benpeart/ada/images/_1a1928ad-4c3a-4578-ae90-0e928d0e105a.jpg

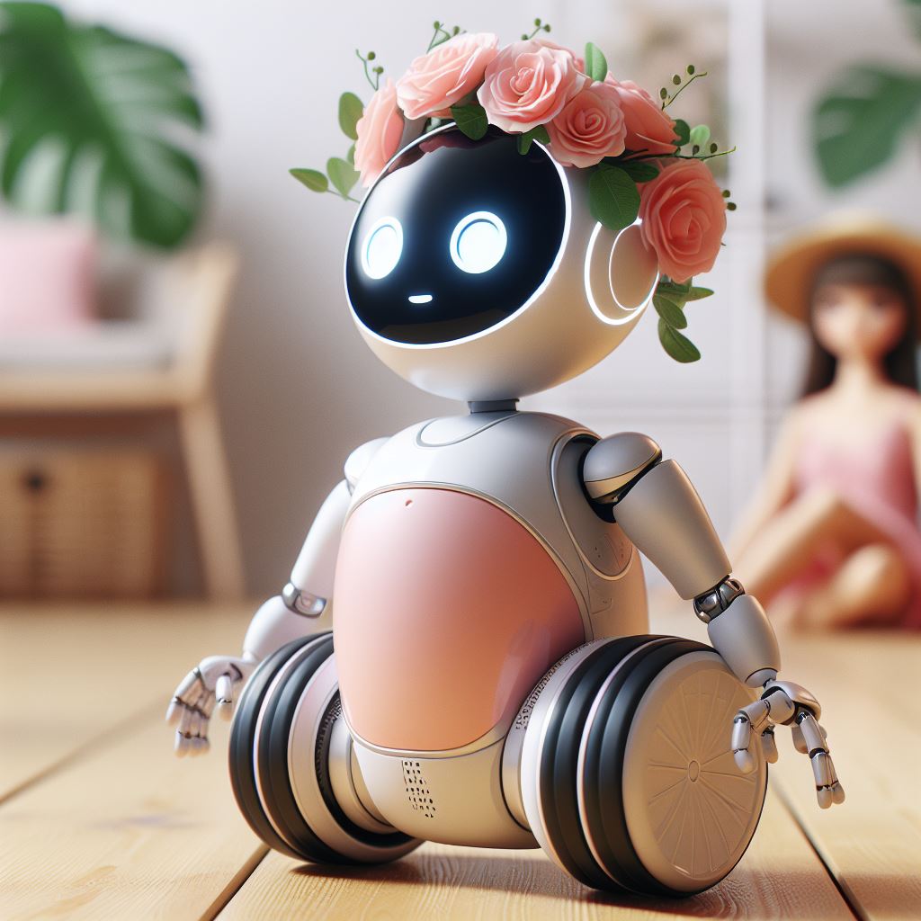
images/_1a1928ad-4c3a-4578-ae90-0e928d0e105a.jpg
