benpeart/ada/images/_2ccc8184-fcf1-47fc-b488-26bac7fec8c7.jpg

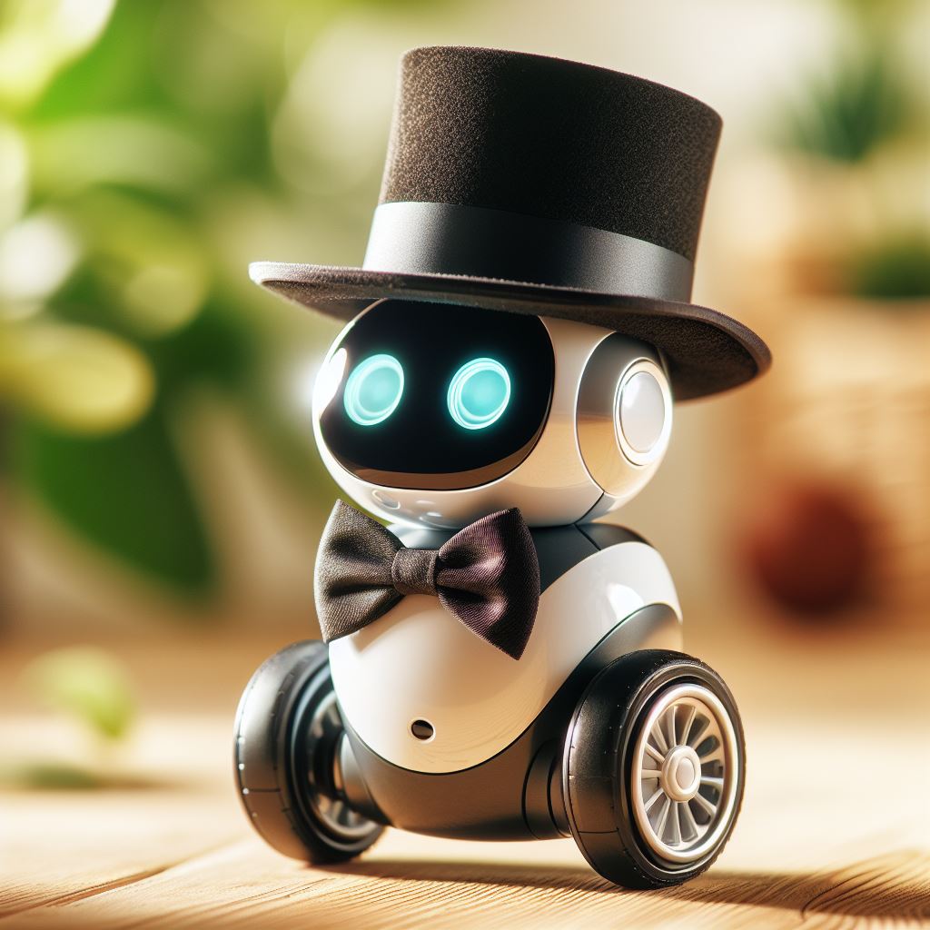
images/_2ccc8184-fcf1-47fc-b488-26bac7fec8c7.jpg
