benpeart/ada/images/_25c779a2-1914-4023-8b9f-634e2caacfa5.jpg

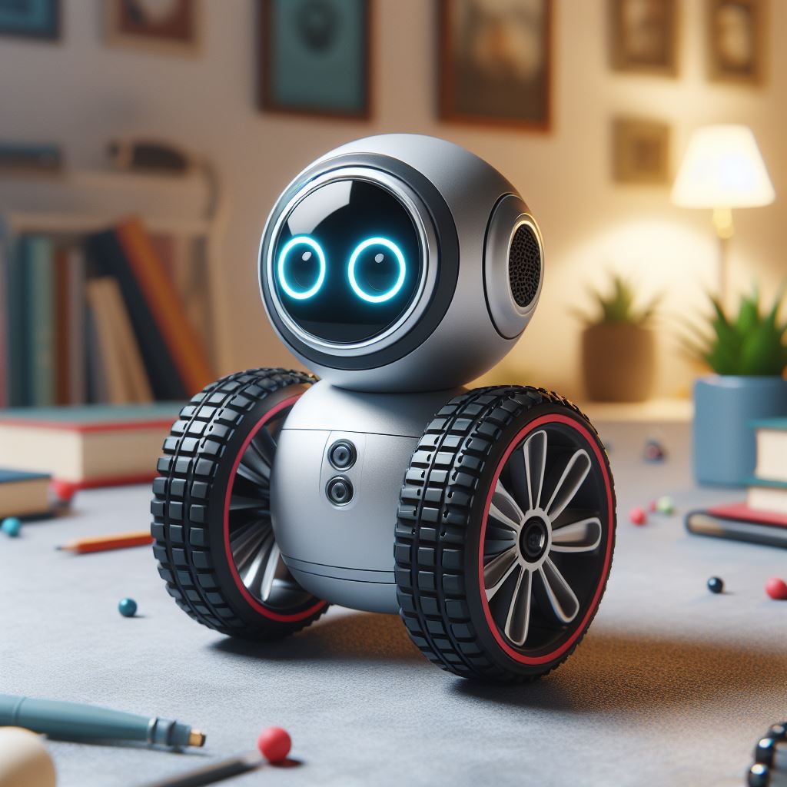
images/_25c779a2-1914-4023-8b9f-634e2caacfa5.jpg
