benpeart/ada/images/_547f5dd5-d0b9-4bb5-aa50-cecd44a33f60.jpg

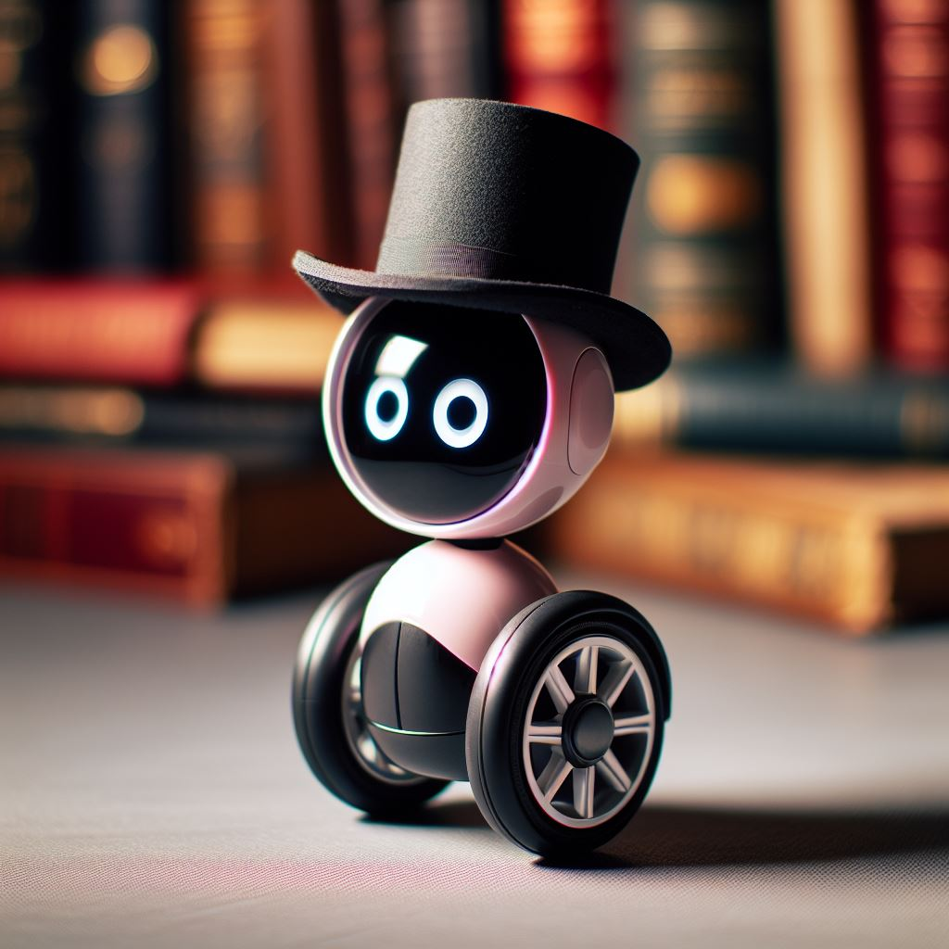
images/_547f5dd5-d0b9-4bb5-aa50-cecd44a33f60.jpg
