benpeart/ada/images/_3496c268-cb07-46fb-8d25-417b17f914ac.jpg

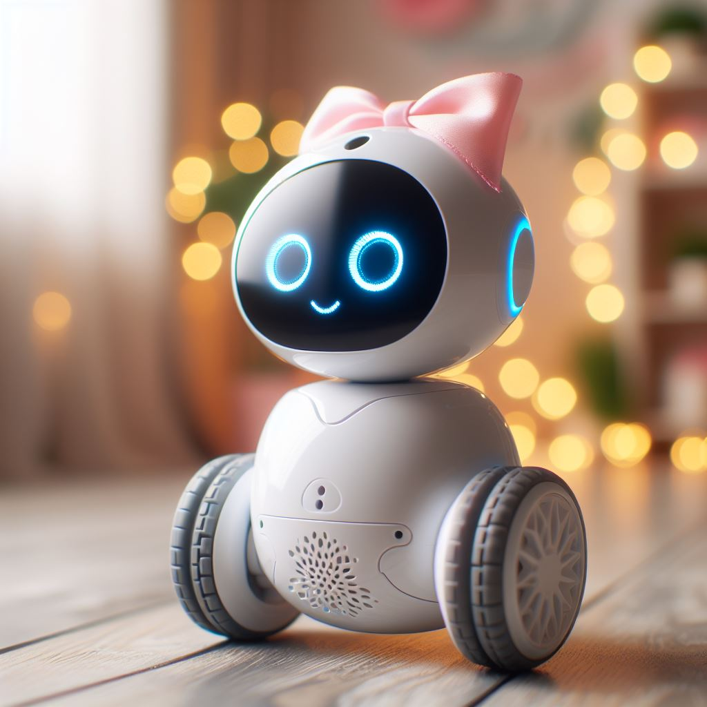
images/_3496c268-cb07-46fb-8d25-417b17f914ac.jpg
