benpeart/ada/images/_54363b42-9e46-489c-88c6-ef07b5f35076.jpg

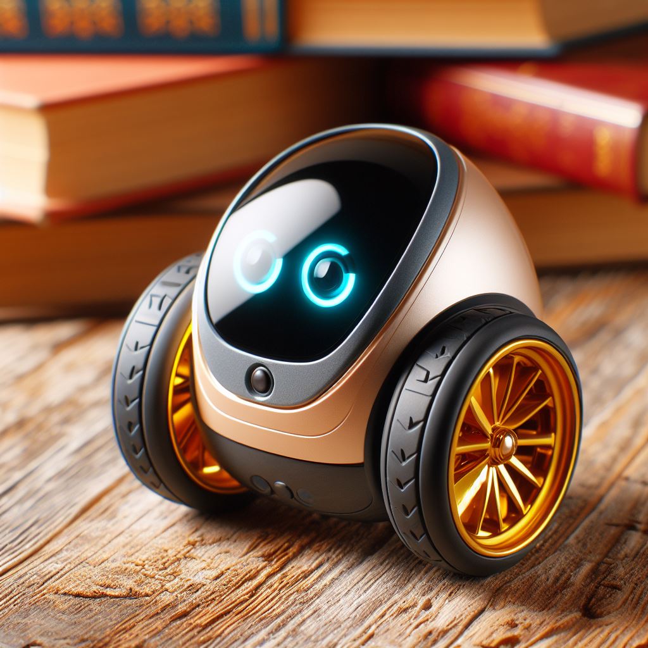
images/_54363b42-9e46-489c-88c6-ef07b5f35076.jpg
