benpeart/ada/images/_815840c3-b298-4146-8053-1009c332dad5.jpg

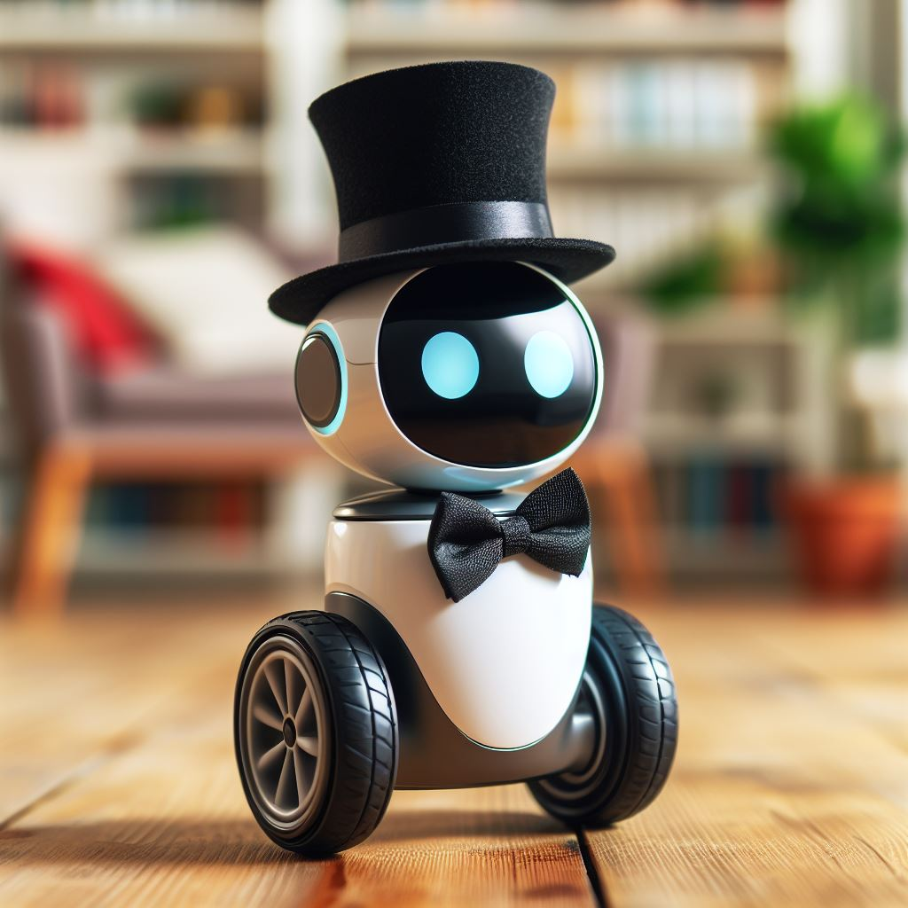
images/_815840c3-b298-4146-8053-1009c332dad5.jpg
