benpeart/ada/images/_acdc5bb5-4fbb-43ef-83b8-d5fd2a900df3.jpg

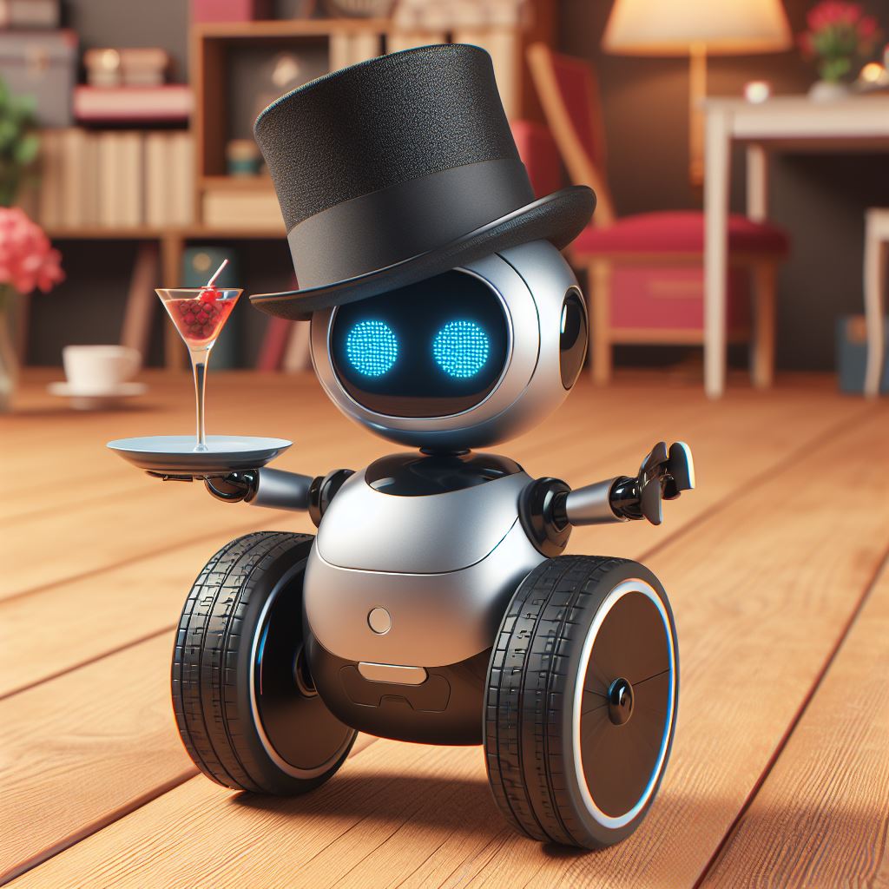
images/_acdc5bb5-4fbb-43ef-83b8-d5fd2a900df3.jpg
