benpeart/ada/images/_df3f3f62-5a5b-451d-bfeb-b59e3f889a02.jpg

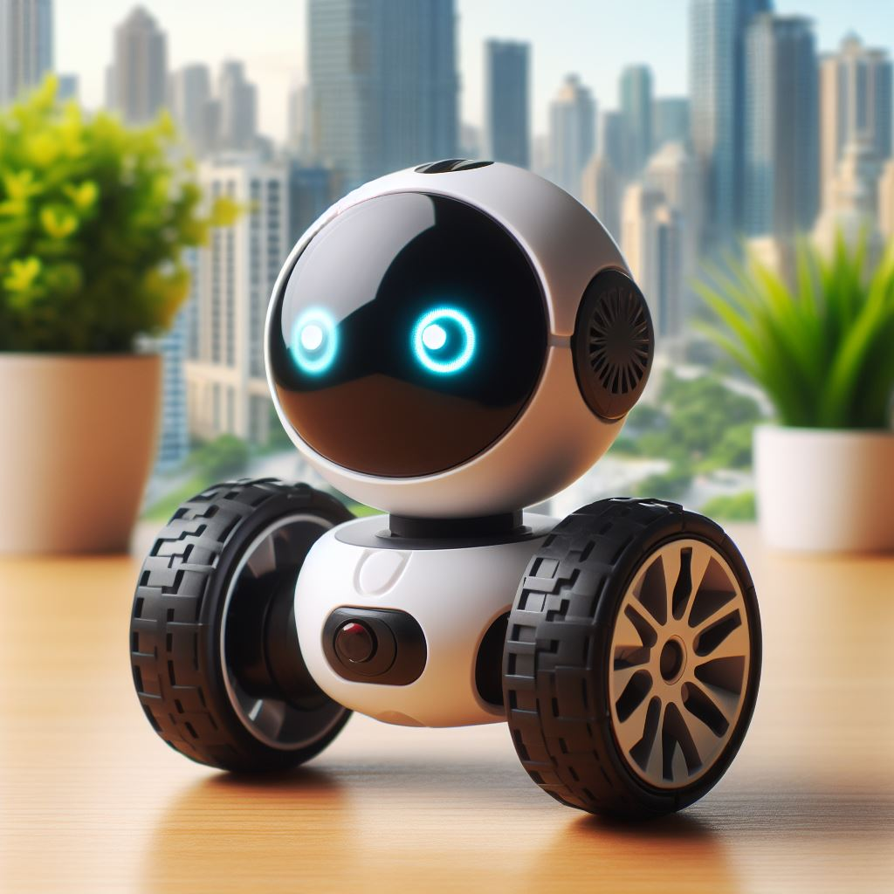
images/_df3f3f62-5a5b-451d-bfeb-b59e3f889a02.jpg
