benpeart/ada/images/_e3b8cc33-37de-4f7d-a31b-75b938612558.jpg

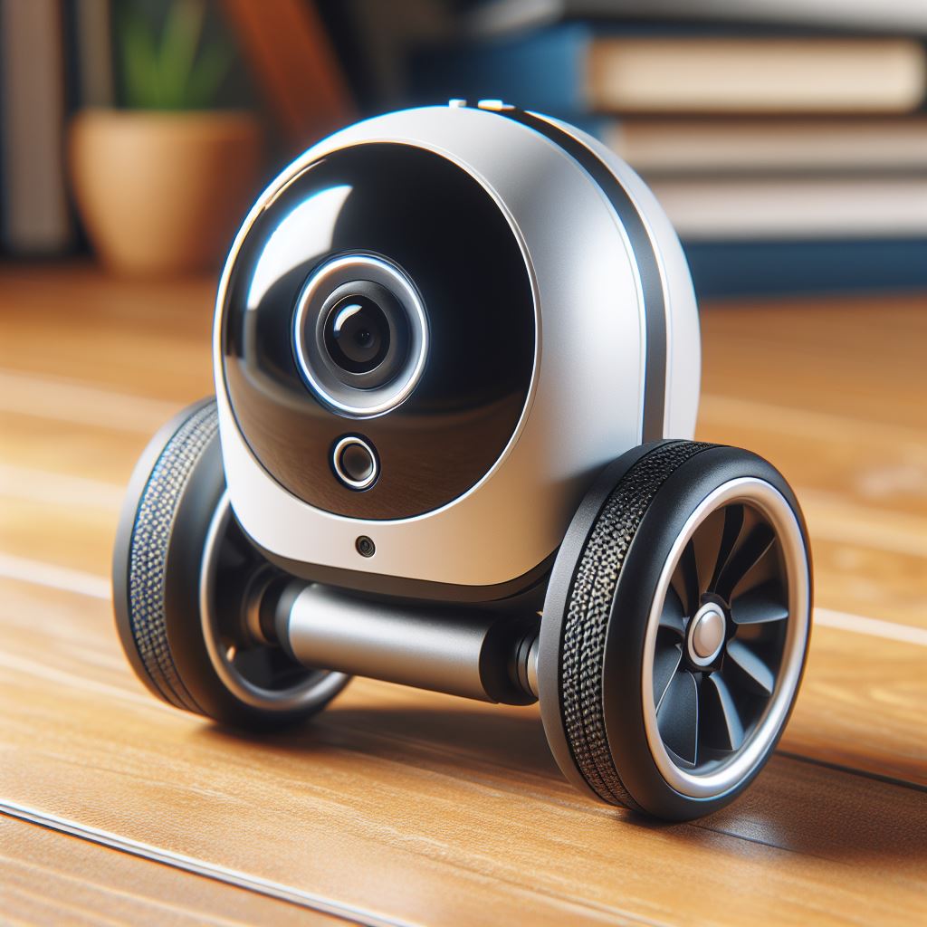
images/_e3b8cc33-37de-4f7d-a31b-75b938612558.jpg
