benpeart/ada/images/PXL_20241112_140447681.PORTRAIT.jpg

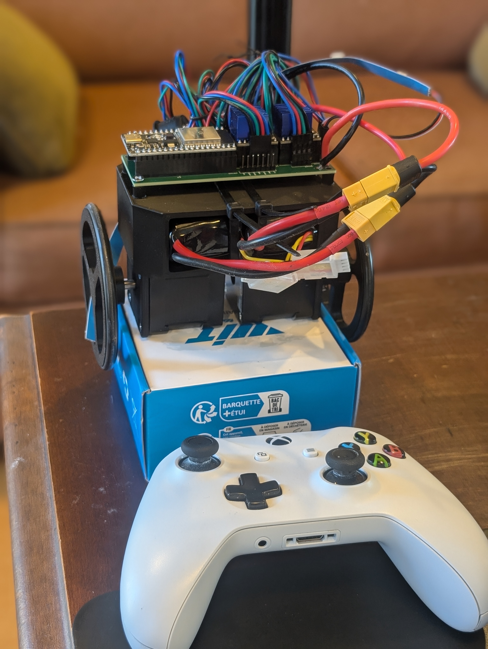
images/PXL_20241112_140447681.PORTRAIT.jpg
