benpeart/ada/Related chip information/ESP32 Dev Board dimensions.jpg

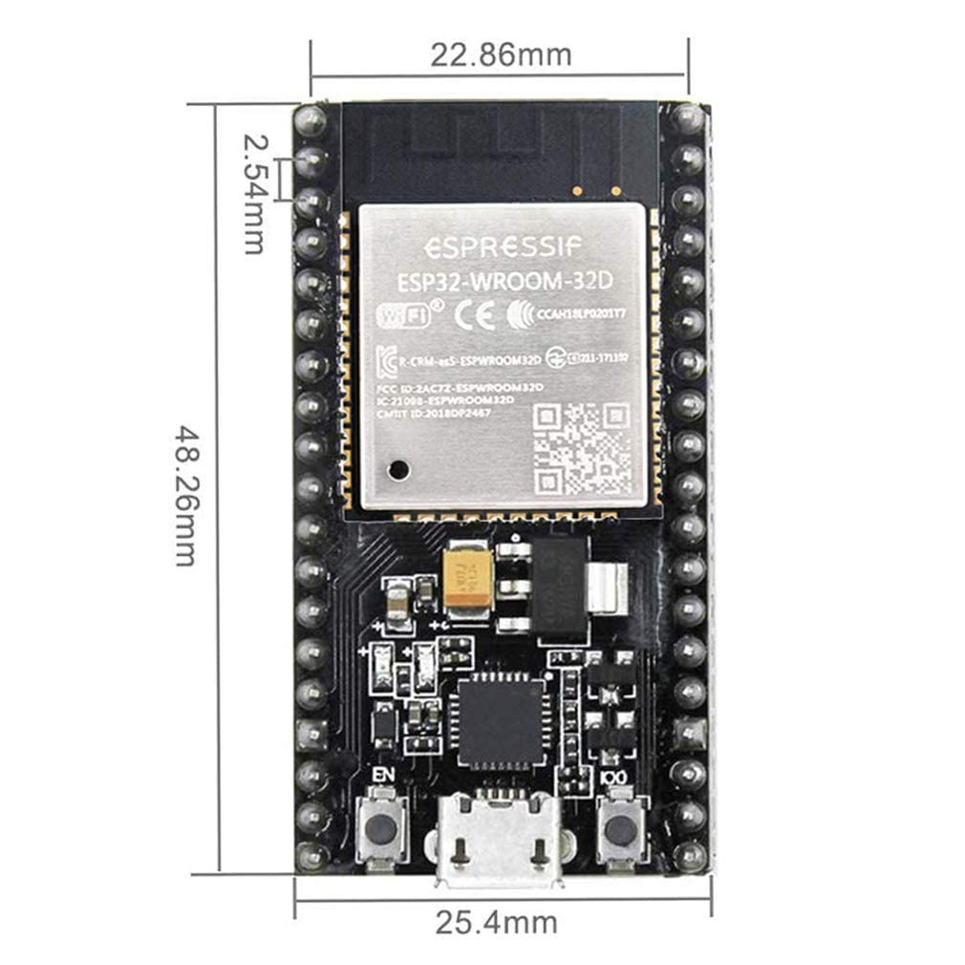
Related chip information/ESP32 Dev Board dimensions.jpg
