benpeart/ada/Related chip information/ESP32 Development Board.jpg

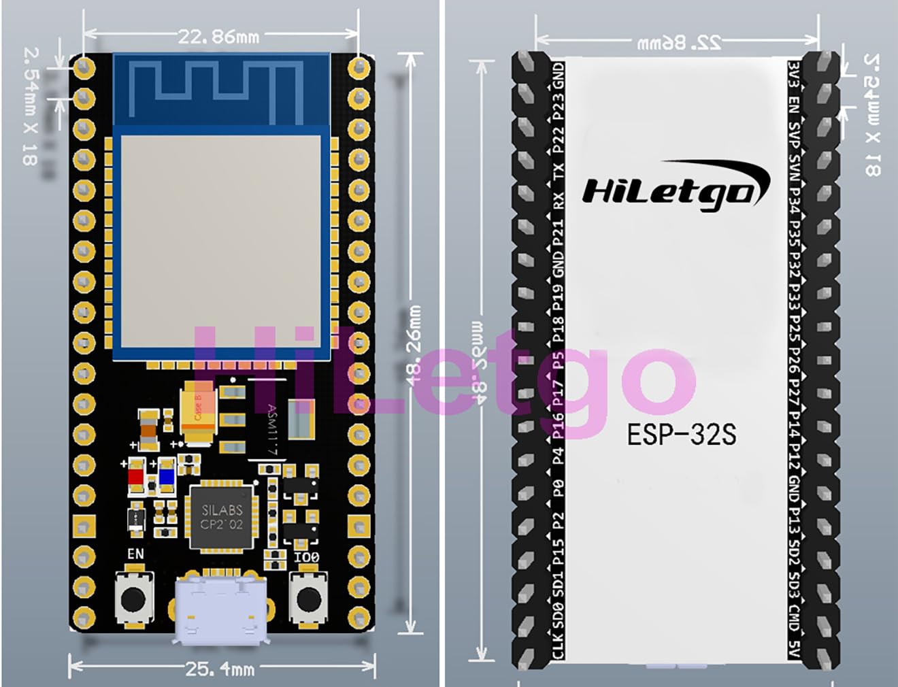
Related chip information/ESP32 Development Board.jpg
