benpeart/ada/Related chip information/ESP32 Pinout.jpg

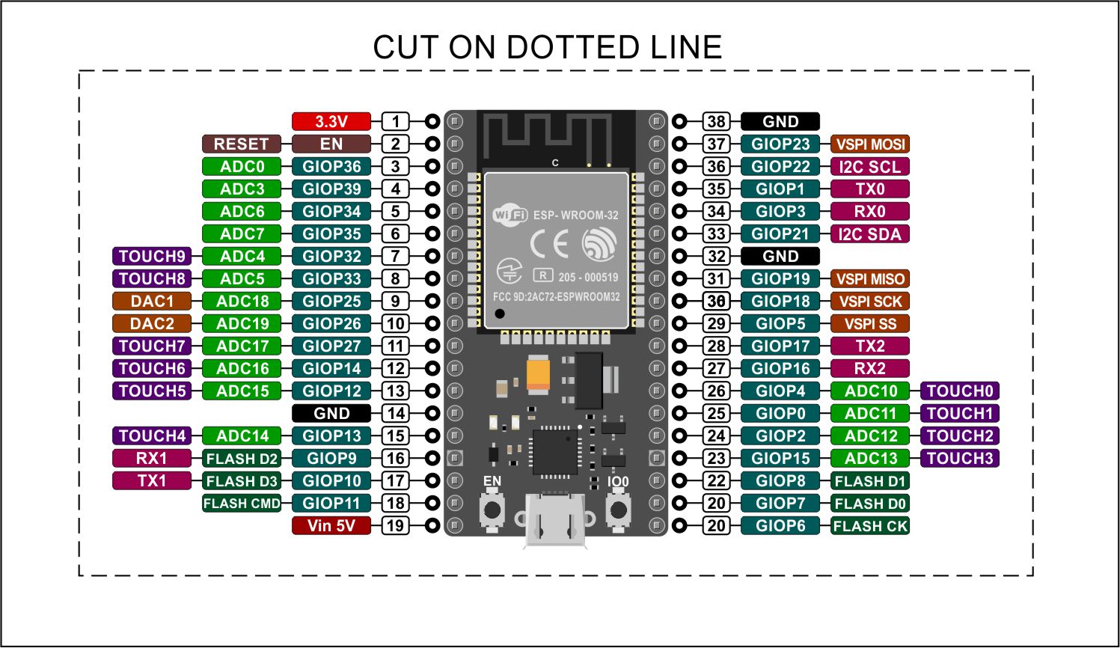
Related chip information/ESP32 Pinout.jpg
