benpeart/ada/Related chip information/ESP-WROOM-32 Auduino IDE settings.jpg

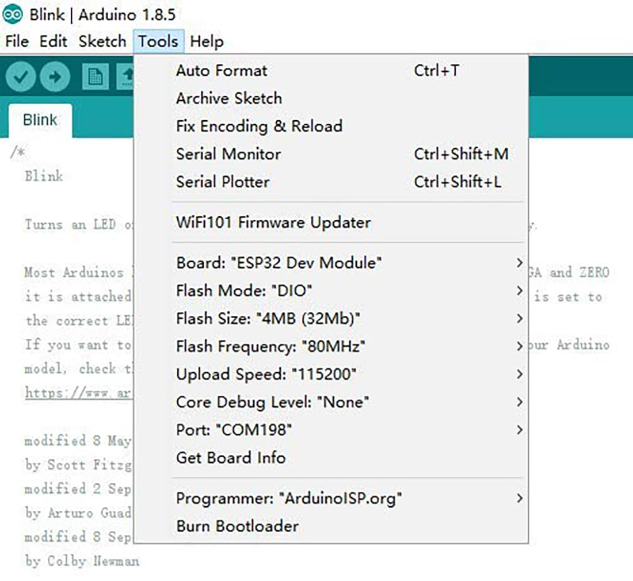
Related chip information/ESP-WROOM-32 Auduino IDE settings.jpg
