benpeart/ada/Related chip information/ESP-WROOM-32D Development Board Schematic.jpg

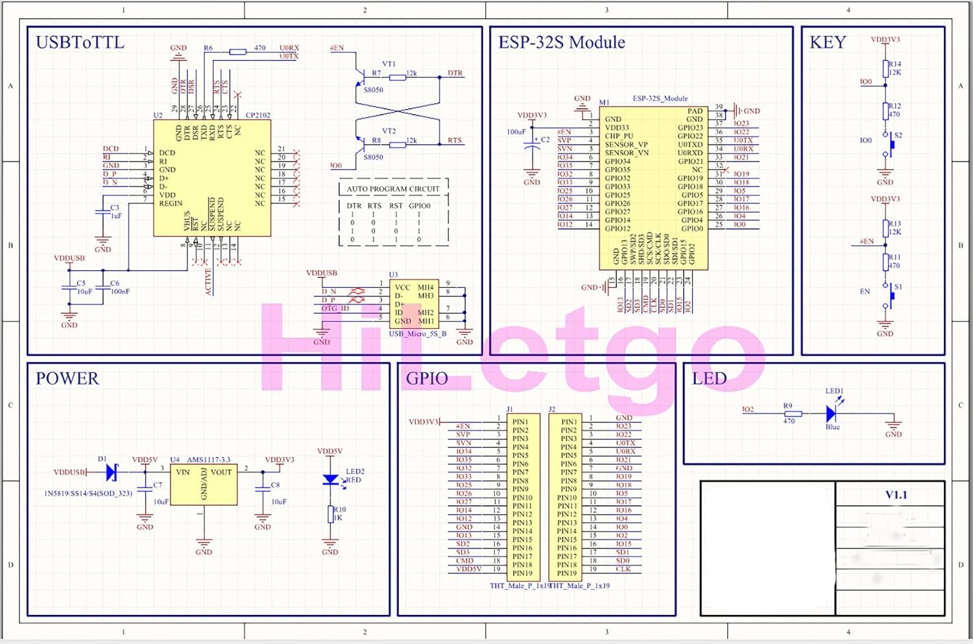
Related chip information/ESP-WROOM-32D Development Board Schematic.jpg
