benpeart/ada/Related chip information/Hoovo 3S1P 120C LiPo Battery with XT60 Plug.jpg

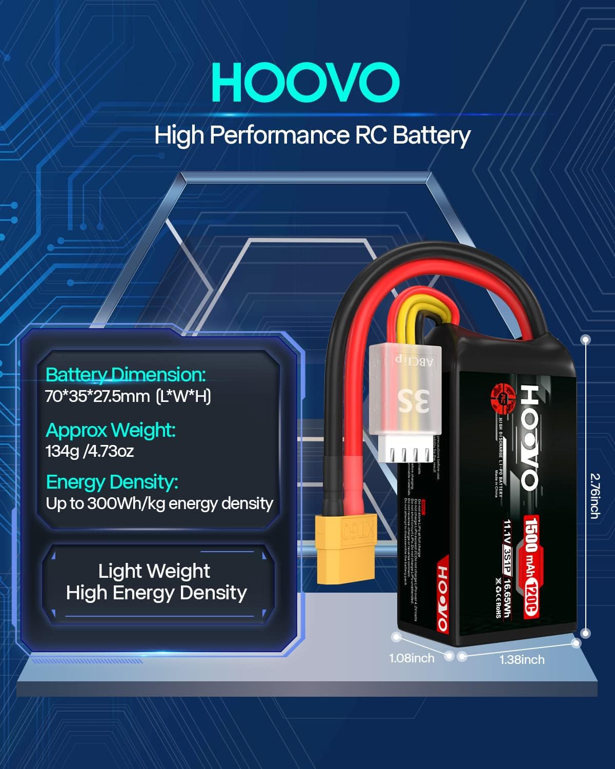
Related chip information/Hoovo 3S1P 120C LiPo Battery with XT60 Plug.jpg
