benpeart/ada/Related chip information/MPU-6050 Pinout.jpg

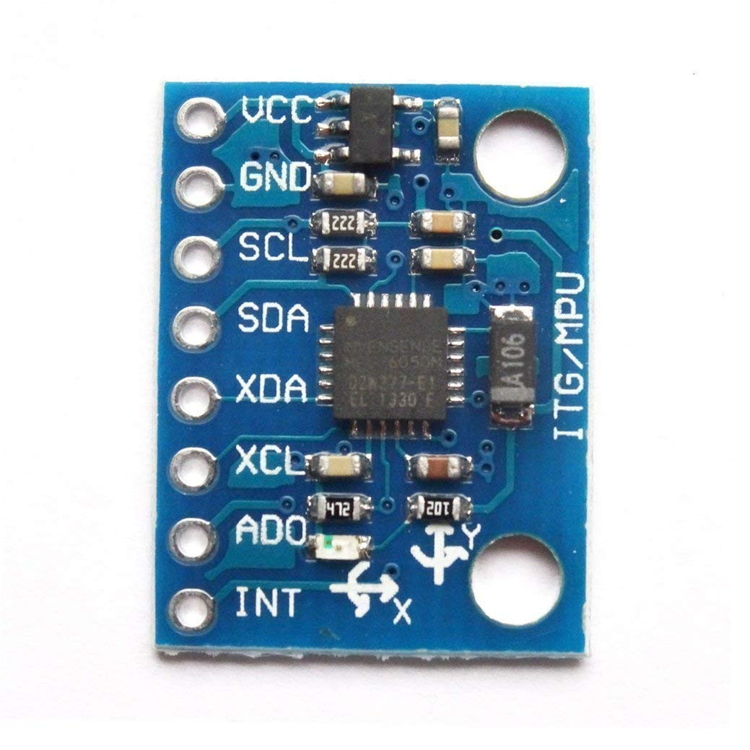
Related chip information/MPU-6050 Pinout.jpg
