benpeart/ada/Related chip information/MPU-6050 Schematic.jpg

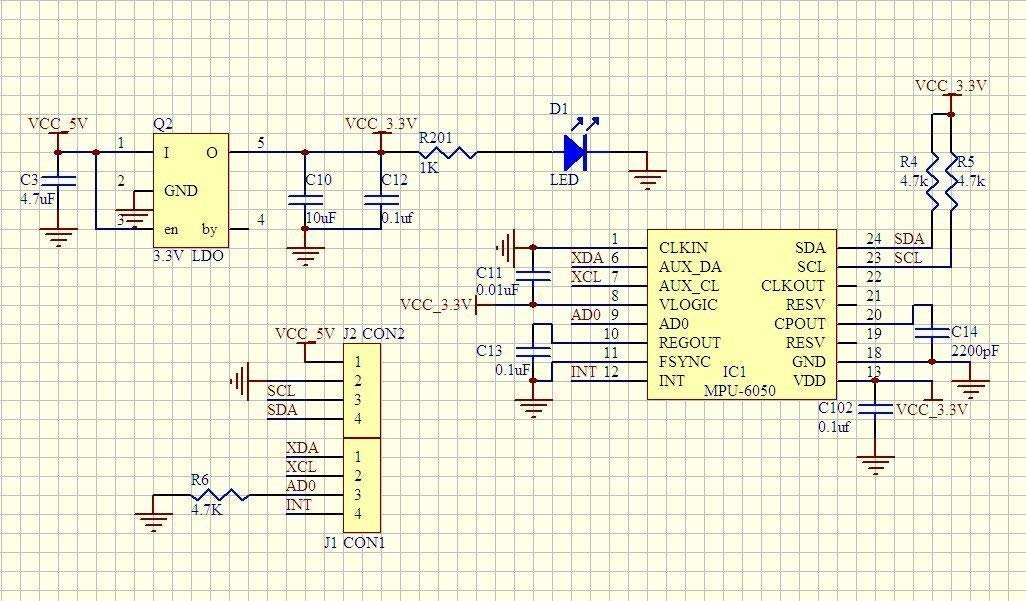
Related chip information/MPU-6050 Schematic.jpg
