benpeart/ada/Related chip information/TMC2209 3D view with heatsink.jpg

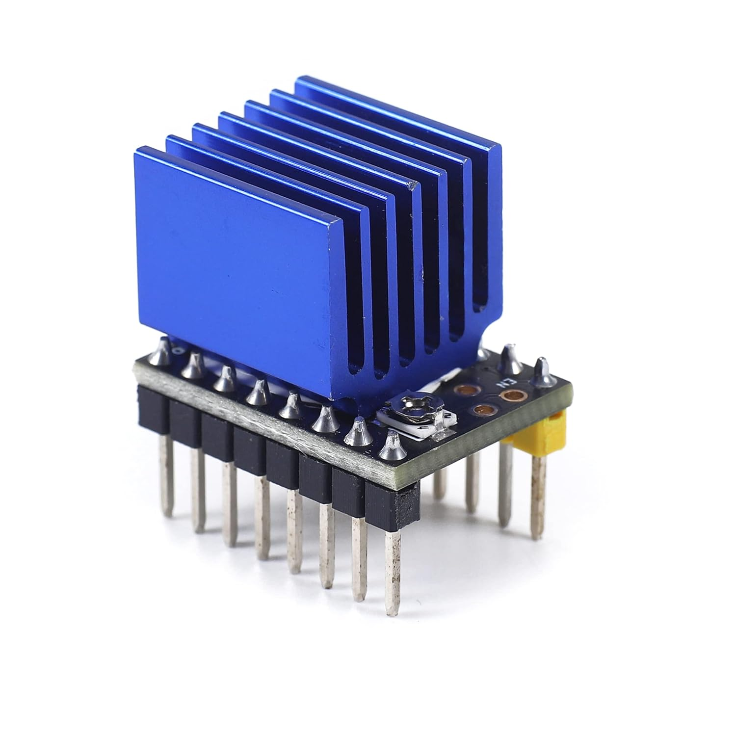
Related chip information/TMC2209 3D view with heatsink.jpg
