benpeart/ada/Related chip information/TMC2209 Pin Function Description.jpg

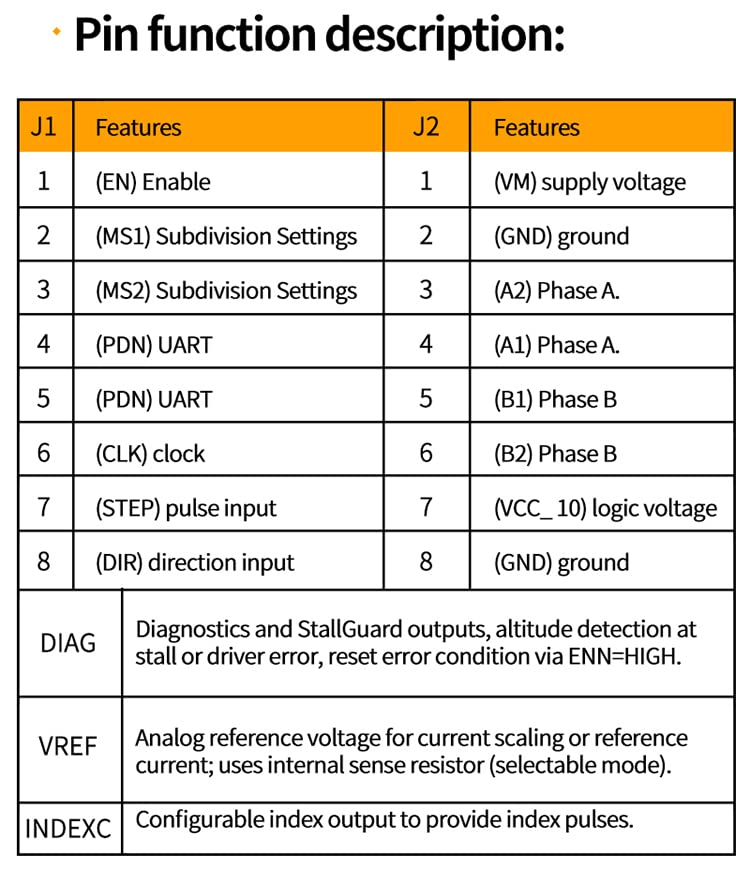
Related chip information/TMC2209 Pin Function Description.jpg
