benpeart/ada/Related chip information/TMC2209 pin side.jpg

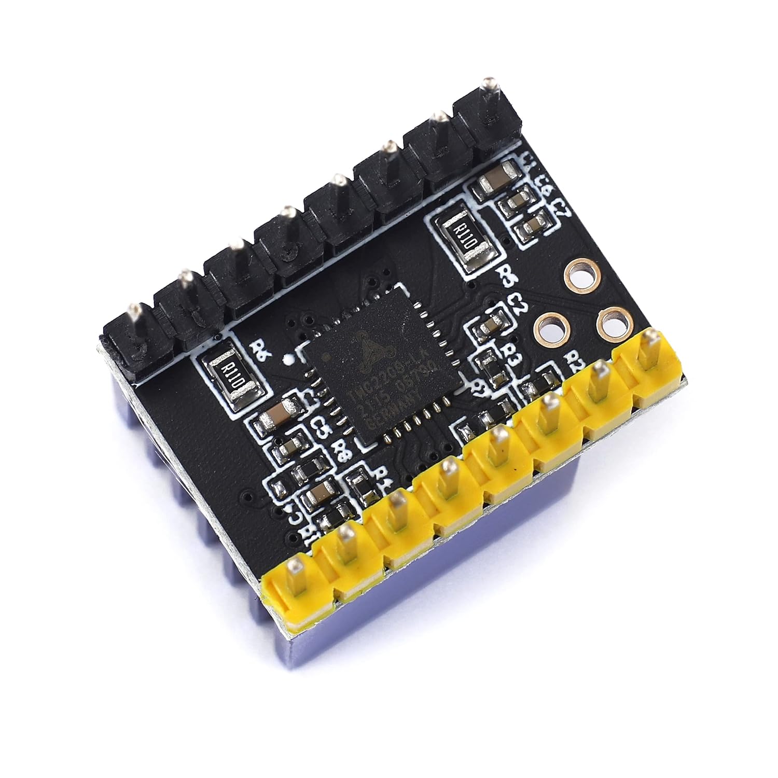
Related chip information/TMC2209 pin side.jpg
