benpeart/ada/Related chip information/TMC2209 Product Parameters.jpg

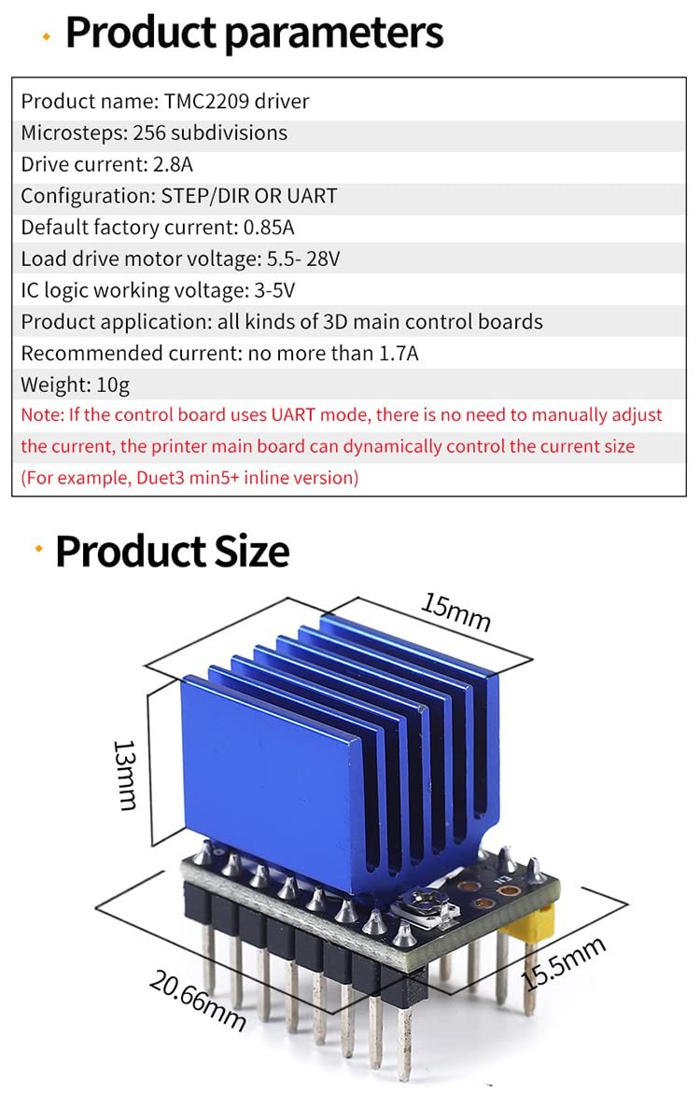
Related chip information/TMC2209 Product Parameters.jpg
