benpeart/ada/Related chip information/TMC2209 Schematic.jpg

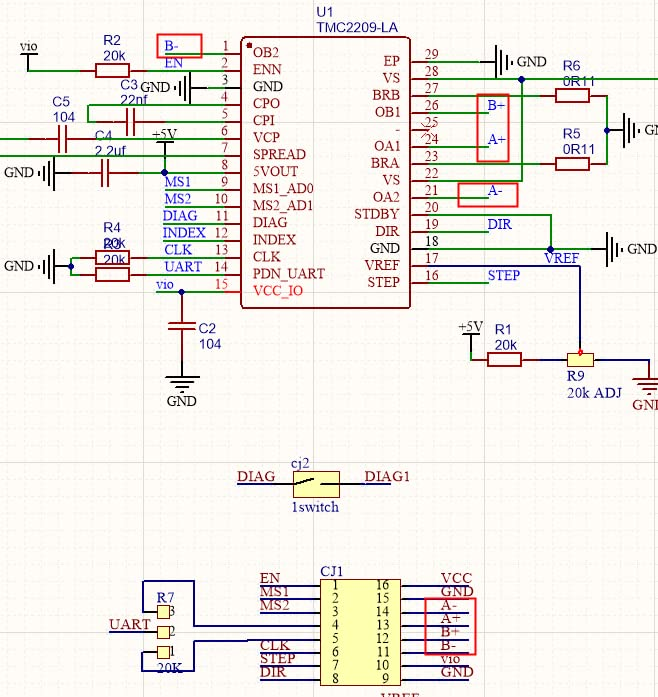
Related chip information/TMC2209 Schematic.jpg
