benpeart/ada/Related chip information/TMC2209 Set Current.jpg

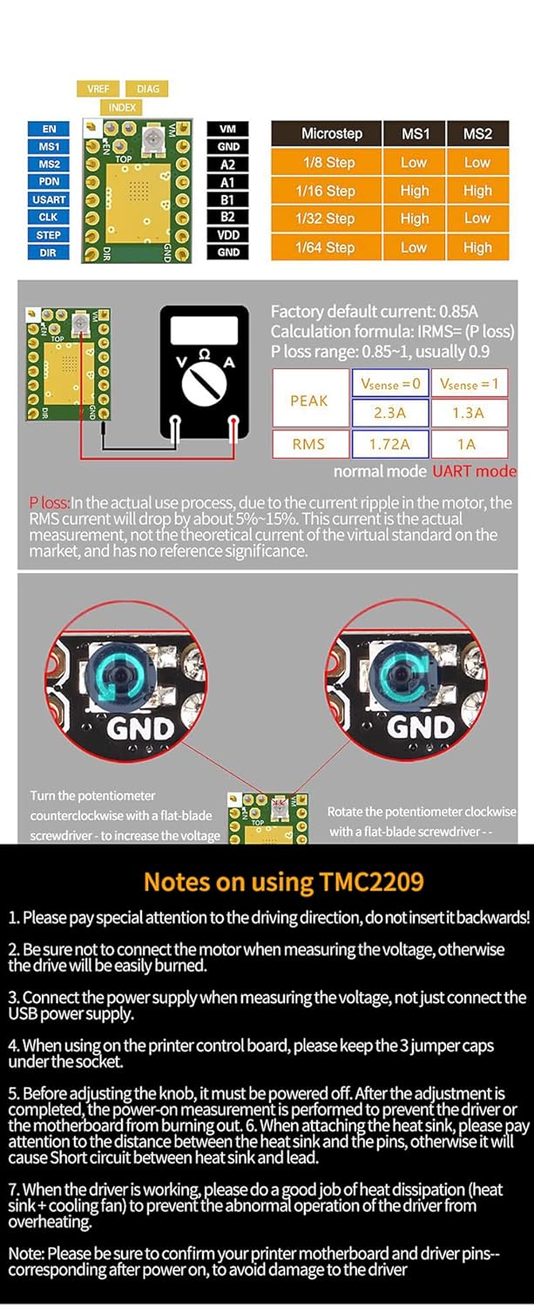
Related chip information/TMC2209 Set Current.jpg
