benpeart/ada/Related chip information/TMC2209 UART Mode Pin Select.jpg

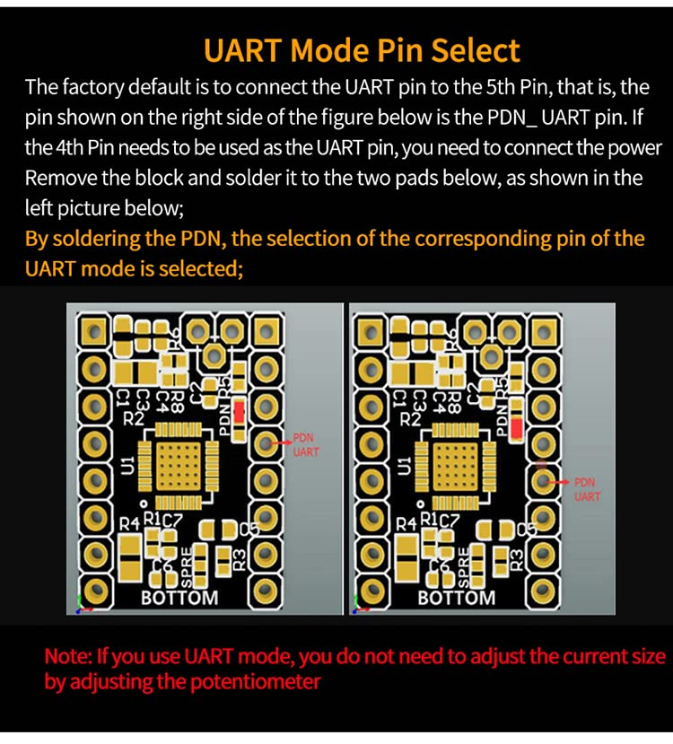
Related chip information/TMC2209 UART Mode Pin Select.jpg
