benpeart/ada/src/globals.h

#ifndef GLOBALS_H
#define GLOBALS_H

// #define WIFI_CONNECTION
// #define WEBSERVER
// #define SERIALINPUT
// #define MDNS // include MDNS support
// #define SPIFFSEDITOR // include the SPPIFFS editor
// #define TMC2209 // TMC2209 stepper controller library (currently broken with V2 hardware, requires powering the TMC2209 logic pin with 3.3V)
// #define DYNAMIC_MICROSTEPPING
// #define DEBUG_SPINNERS
// #define INPUT_PS3  // PS3 controller via bluetooth. Dependencies take up quite some program space!
#define INPUT_XBOX // Xbox controller via bluetooth. Dependencies take up quite some program space!
#define LED_LIGHTS
#define BATTERY_VOLTAGE
#define FALL_DETECTION

#include <Arduino.h>
#include <Preferences.h>

// ESP32 Pin Assignments

// Stepper motor pin assignments
#define motEnablePin 27

#define motLeftUStepPin1 19
#define motLeftUStepPin2 18
#define motLeftStepPin 26
#define motLeftDirPin 25

#define motRightUStepPin1 05
#define motRightUStepPin2 04
#define motRightStepPin 33
#define motRightDirPin 32

// TMC2209 Stepper driver
#define SERIAL2_RX_PIN 16    // Specify Serial2 RX pin as the default has changed
#define SERIAL2_TX_PIN 17    // Specify Serial2 TX pin as the default has changed

// -- Others
#define PIN_LED_DATA 02        // pin to the data line of WS2812 LEDs
#define PIN_BATTERY_VOLTAGE 36 // ADC pin connected to voltage divider

#define PIN_I2C_SDA 21       // MPU SDA pin
#define PIN_I2C_SCL 22       // MPU SCL pin
#define PIN_MPU_INTERRUPT 23 // MPU interrupt pin

extern Preferences preferences;

/*  Remote control structure
    Every remote should give a speed and steer command from -100 ... 100
    To adjust "driving experience", e.g. a slow beginners mode, or a fast expert mode, a gain can be adjusted for the speed and steer inputs.
    Additionaly, a selfRight input can be used. When setting this bit to true, the robot will enable control in an attempt to self right.
    The disable control input can be used to
        1) disable the balancing mode
        2) disable the self-right attempt
    Depending on which state the robot is in.
*/
typedef struct
{
    float speed = 0;
    float steer = 0;
    float speedGain = 0.7;
    float steerGain = 0.6;
    float speedOffset = 0.0;
    bool selfRight = false;
    bool disableControl = false;
} remoteControlType;
extern remoteControlType remoteControl;

#endif // GLOBALS_H
